acwright/6502-VCS/Models/240-1280-00-0602J.step

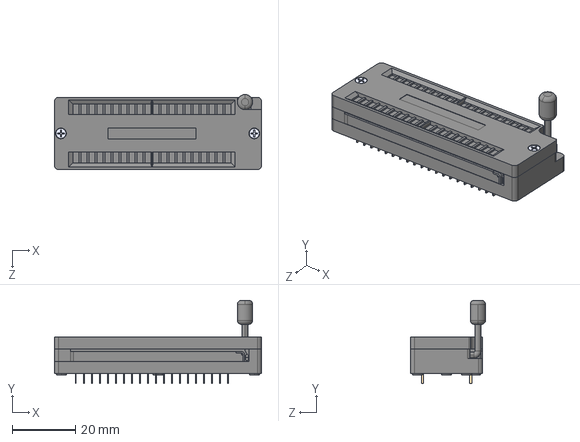
[picture p19: CAD file, 2026-05-03]
Models/240-1280-00-0602J.step
65.5 x 26.4 x 23.7 mm
