acwright/6502-VCS/Models/0702461201.step

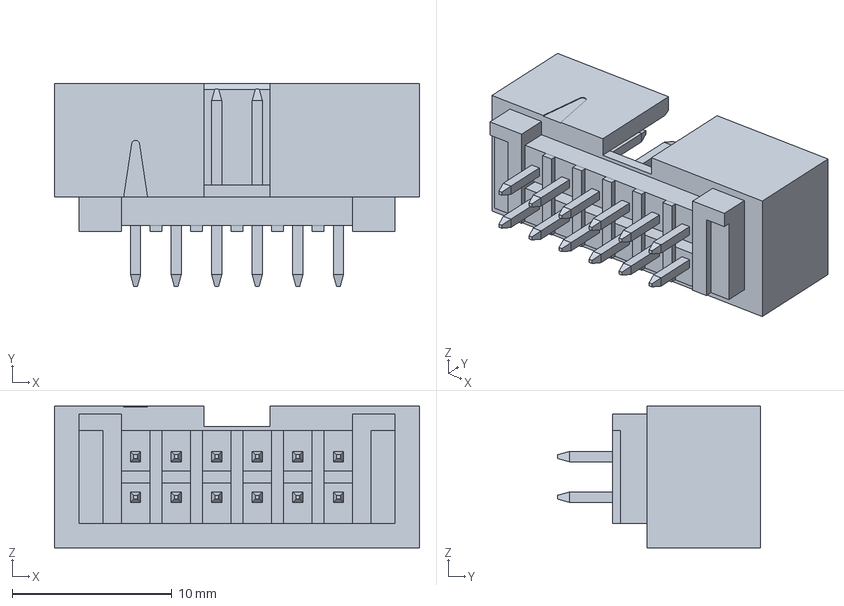
[picture p20: CAD file, 2026-05-03]
Models/0702461201.step
22.9 x 12.7 x 8.89 mm
